geojenks/braille-tip/docs/instructables/sketch_parts_exploded.png

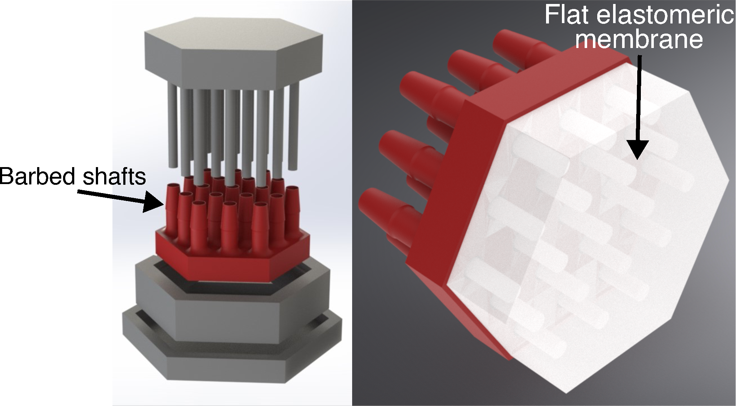
docs/instructables/sketch_parts_exploded.png
