geojenks/braille-tip/docs/instructables/sketch_parts_exploded_2.png

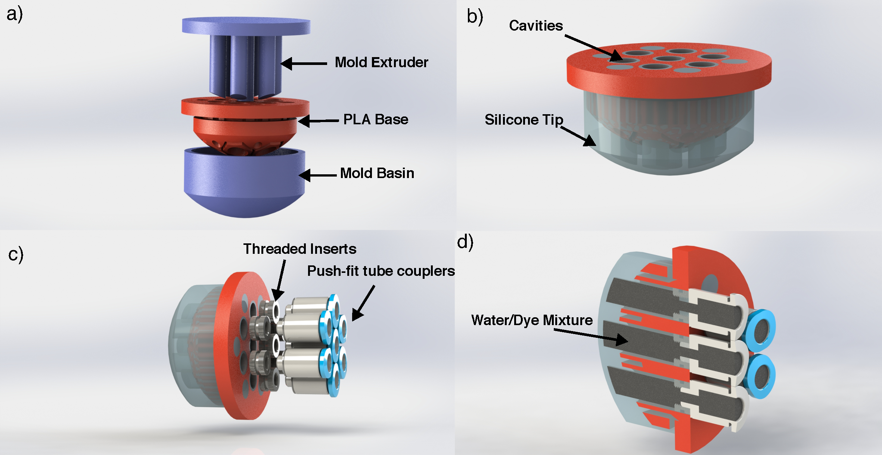
docs/instructables/sketch_parts_exploded_2.png
