geojenks/braille-tip/docs/instructables/arduino_wiring.jpeg

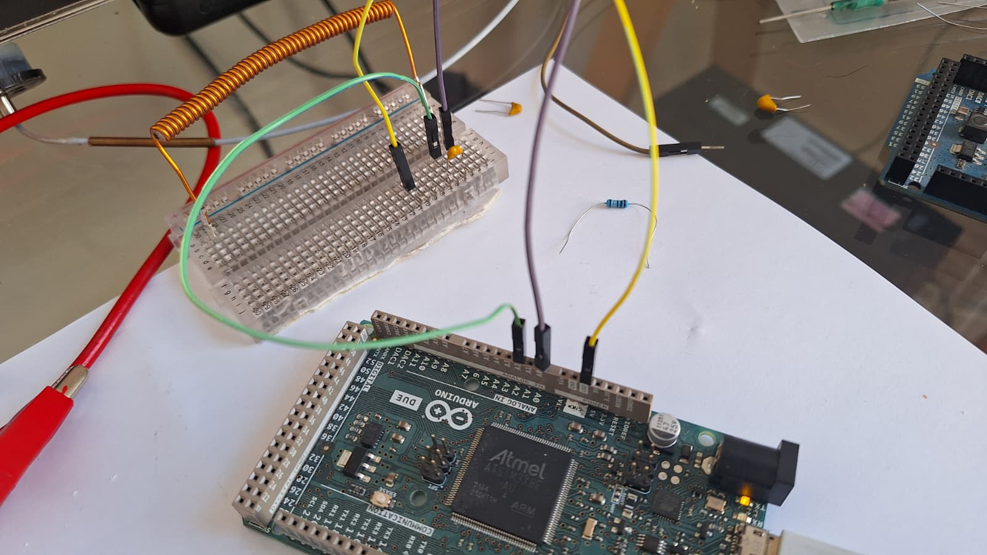
docs/instructables/arduino_wiring.jpeg
