geojenks/braille-tip/docs/instructables/comparison_photo.jpeg

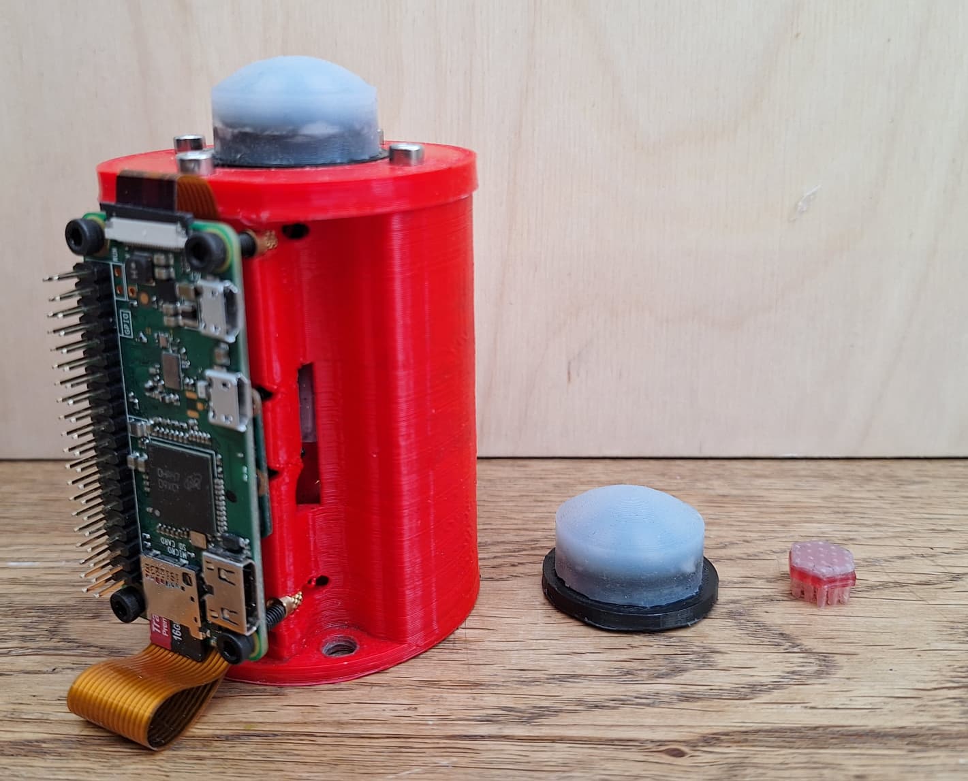
docs/instructables/comparison_photo.jpeg
