geojenks/braille-tip/docs/instructables/model_vs_exp.png

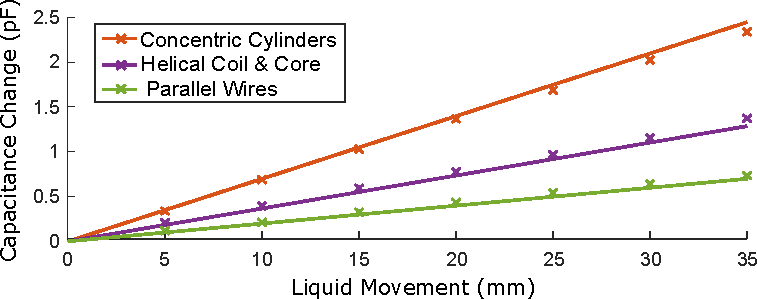
docs/instructables/model_vs_exp.png
