geojenks/braille-tip/docs/instructables/nicely_contained_LM.jpeg

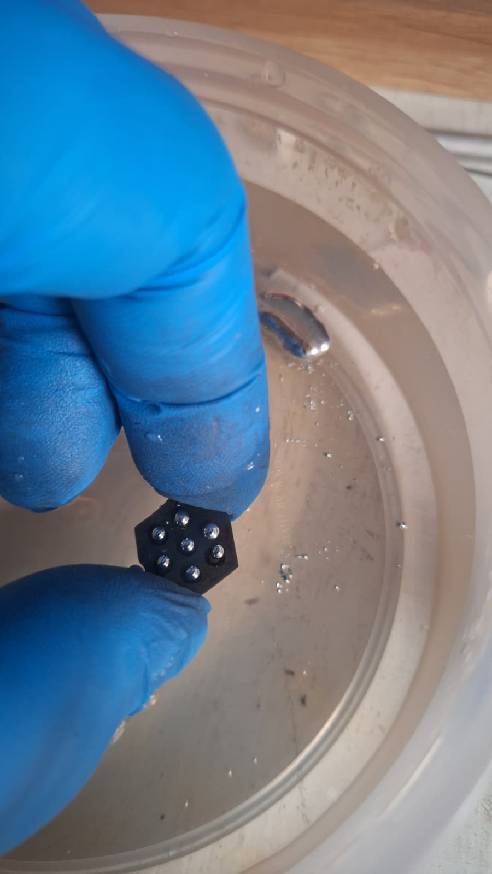
docs/instructables/nicely_contained_LM.jpeg
