geojenks/braille-tip/docs/instructables/printed_tip_and_backing.png

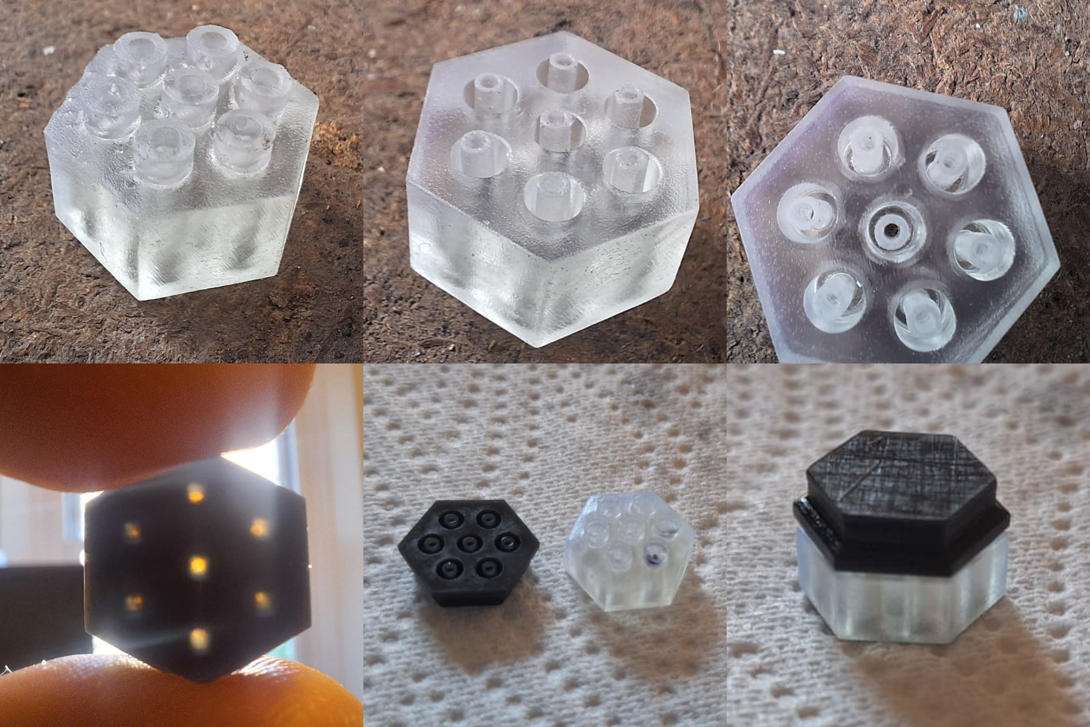
docs/instructables/printed_tip_and_backing.png
