geojenks/braille-tip/docs/instructables/scale_example.png

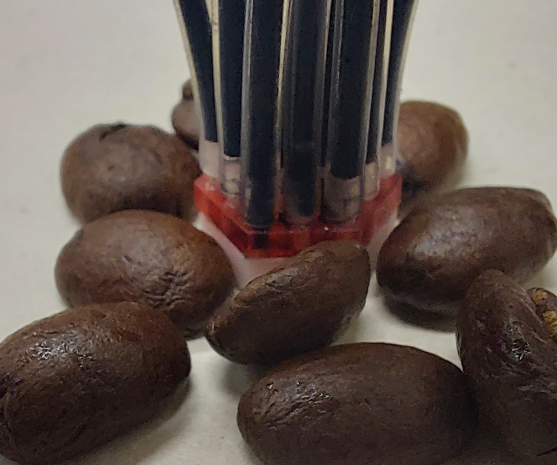
docs/instructables/scale_example.png
