geojenks/braille-tip/docs/instructables/sketch_fab_flow_process.png

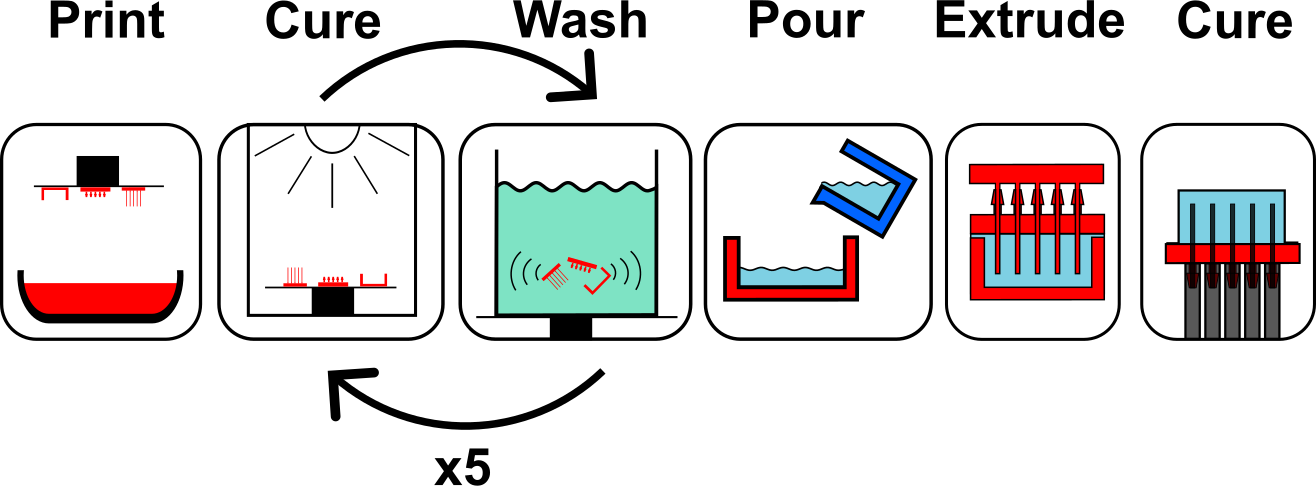
docs/instructables/sketch_fab_flow_process.png
