geojenks/braille-tip/docs/instructables/to_binary.png

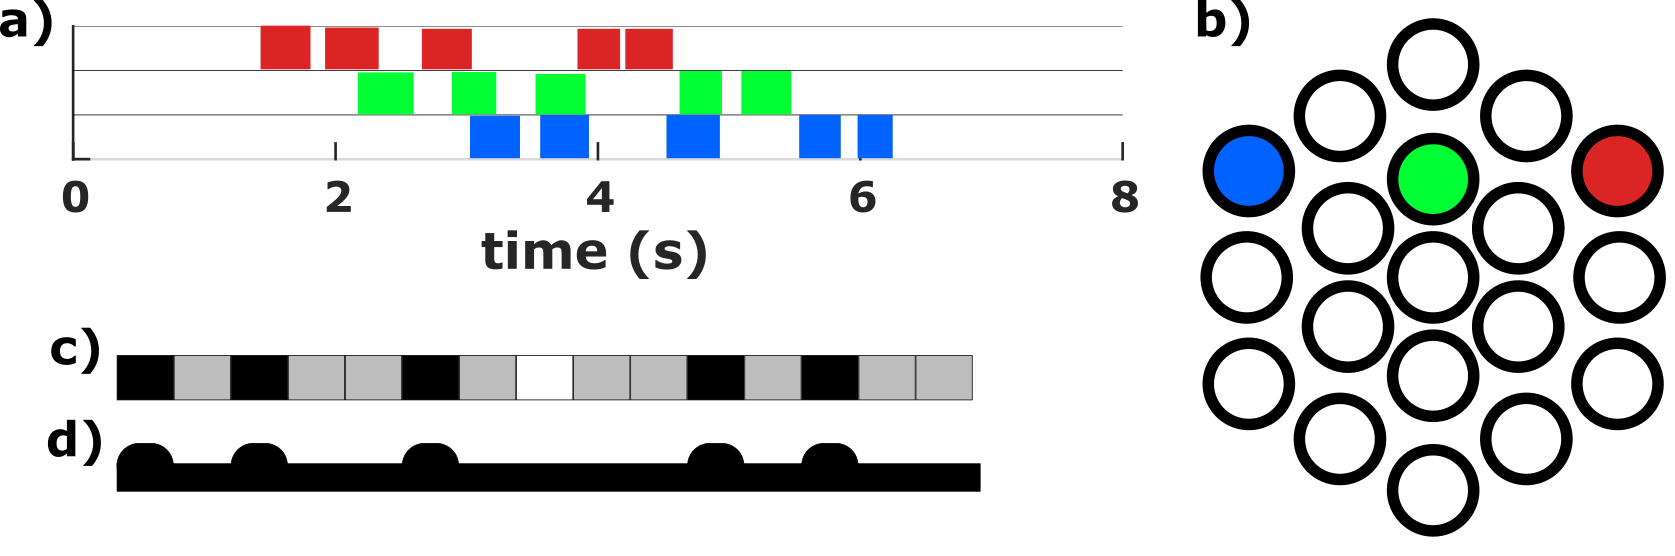
docs/instructables/to_binary.png
