geojenks/braille-tip/docs/instructables/tubing_barbs.png

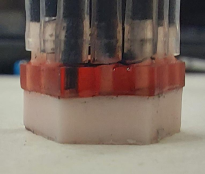
docs/instructables/tubing_barbs.png
