geojenks/braille-tip/docs/instructables/Braille_result.png

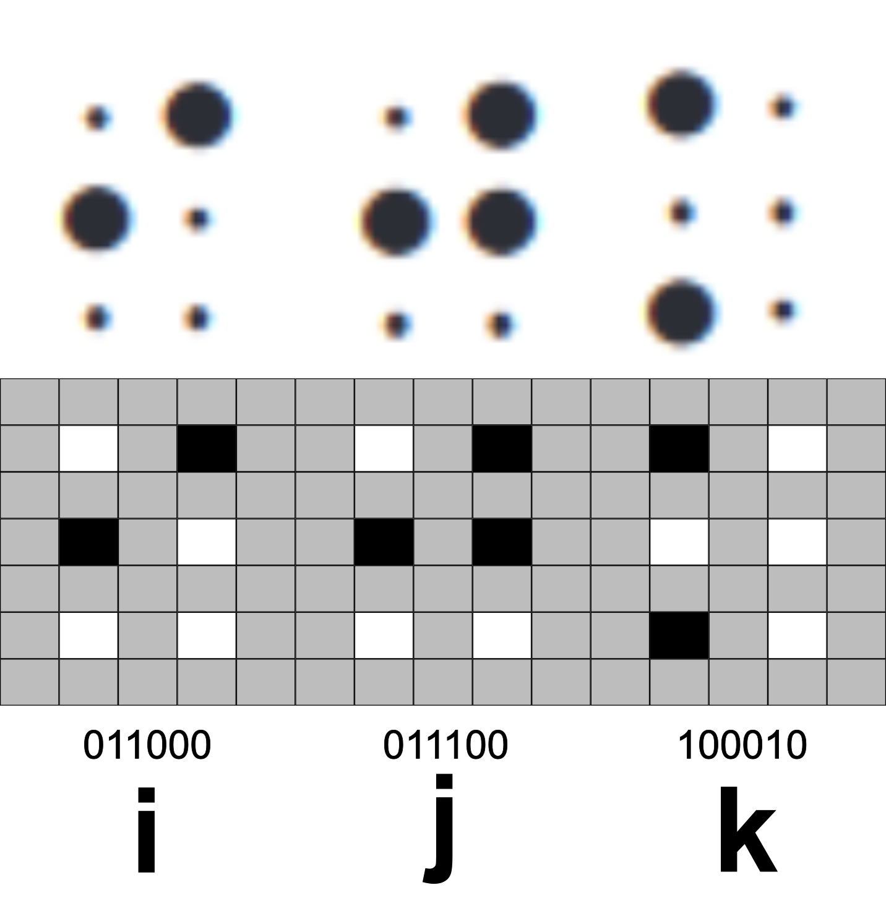
docs/instructables/Braille_result.png
