geojenks/braille-tip/docs/instructables/Cap_calibration_bottom.png

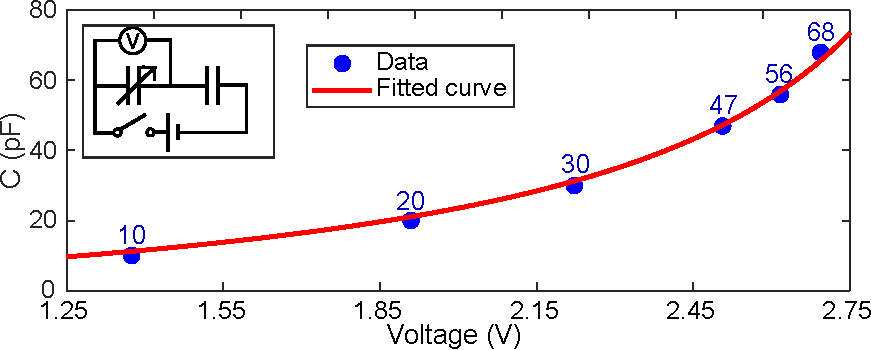
docs/instructables/Cap_calibration_bottom.png
